OxFloodNet/sensor-device/OXFloodNet_Dispay/logo.h

// Settings are Orientation: Horizontal
// Byte order: LSB First
//const unsigned char OxFloodNet[] = {
static const unsigned char OxFloodNet[] PROGMEM = {
    '\x00','\x00','\x00','\x00','\x00','\x00','\x00','\x00', // 0x0008
    '\x00','\x00','\x00','\x00','\x00','\x00','\x00','\x00', // 0x0018
    '\x00','\x00','\x00','\x00','\x00','\x00','\x00','\x00', // 0x0028
    '\x00','\x00','\x00','\x00','\x00','\x00','\x00','\x00', // 0x0038
    '\x00','\x00','\x00','\x00','\x00','\x00','\x00','\x00', // 0x0048
    '\x00','\x00','\x00','\x00','\x00','\x00','\x00','\x00', // 0x0058
    '\x00','\x00','\x00','\x00','\x00','\x00','\x00','\x00', // 0x0068
    '\x00','\x00','\x00','\x00','\x00','\x00','\x00','\x00', // 0x0078
    '\x00','\x00','\x00','\x00','\x00','\x00','\x00','\x00', // 0x0088
    '\x00','\x00','\x00','\x00','\x00','\x00','\x00','\x00', // 0x0098
    '\x00','\x00','\x00','\x00','\x00','\x00','\x00','\x00', // 0x00a8
    '\x00','\x00','\x00','\x00','\x00','\x00','\x00','\x00', // 0x00b8
    '\x00','\x00','\x00','\x00','\x00','\x00','\x00','\x00', // 0x00c8
    '\x00','\x00','\x00','\x00','\x00','\x00','\x00','\x00', // 0x00d8
    '\x00','\x00','\x00','\x00','\x00','\x00','\x00','\x00', // 0x00e8
    '\x00','\x00','\x00','\x00','\x00','\x00','\x00','\x00', // 0x00f8
    '\x00','\x00','\x00','\x00','\x00','\x00','\x00','\x00', // 0x0108
    '\x00','\x00','\x00','\x00','\x00','\x00','\x00','\x00', // 0x0118
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
    '\x00','\x01','\xff','\xff','\xff','\xff','\xff','\xff', // 0x0848
    '\xff','\xf8','\x00','\x38','\x00','\x00','\x30','\x00', // 0x0858
    '\x00','\x01','\xff','\xff','\xff','\xff','\xff','\xff', // 0x0868
    '\xff','\xf8','\x00','\x78','\x00','\x00','\x38','\x00', // 0x0878
    '\x00','\x01','\xff','\xff','\xff','\xff','\xff','\xff', // 0x0888
    '\xff','\xf8','\x00','\xf0','\x00','\x00','\x38','\x00', // 0x0898
    '\x00','\x01','\xff','\xff','\xff','\xff','\xff','\xff', // 0x08a8
    '\xff','\xf8','\x03','\xff','\x00','\x00','\x38','\x00', // 0x08b8
    '\x00','\x01','\xff','\xff','\xff','\xff','\xff','\xff', // 0x08c8
    '\xff','\xf8','\x03','\xff','\xfe','\x00','\x18','\x00', // 0x08d8
    '\x00','\x01','\xff','\xff','\xff','\xff','\xff','\xff', // 0x08e8
    '\xff','\xf8','\x07','\xff','\xff','\xf8','\x1c','\x00', // 0x08f8
    '\x00','\x01','\xff','\xff','\xff','\xff','\xff','\xff', // 0x0908
    '\xff','\xf8','\x07','\x8f','\xff','\xff','\xfc','\x00', // 0x0918
    '\x00','\x01','\xff','\xff','\xff','\xff','\xff','\xff', // 0x0928
    '\xff','\xf8','\x07','\x07','\xff','\xff','\xfe','\x00', // 0x0938
    '\x00','\x01','\xff','\xff','\xff','\xff','\xff','\xff', // 0x0948
    '\xff','\xf8','\x07','\x07','\xff','\xff','\xff','\x00', // 0x0958
    '\x00','\x01','\xff','\xff','\xff','\xff','\xff','\xff', // 0x0968
    '\xff','\xf8','\x07','\x0f','\xff','\xff','\xdf','\x00', // 0x0978
    '\x00','\x01','\xff','\xff','\xff','\xff','\xff','\xff', // 0x0988
    '\xff','\xf8','\x0f','\xdf','\xff','\xff','\x87','\x80', // 0x0998
    '\x00','\x01','\x87','\xff','\xff','\xff','\xff','\xff', // 0x09a8
    '\xff','\xf8','\x0f','\xff','\xff','\xe1','\x07','\x80', // 0x09b8
    '\x00','\x00','\x00','\x7f','\xff','\xf0','\x03','\xff', // 0x09c8
    '\xff','\xc0','\x0f','\xff','\xfe','\x00','\x07','\x00', // 0x09d8
    '\x00','\x00','\x00','\x1f','\xff','\xc0','\x00','\xff', // 0x09e8
    '\xfe','\x00','\x03','\xff','\xf0','\x00','\x07','\x00', // 0x09f8
    '\x00','\x00','\x00','\x07','\xfe','\x00','\x00','\x1f', // 0x0a08
    '\xf8','\x00','\x00','\xff','\xc0','\x00','\x03','\x00', // 0x0a18
    '\x00','\x00','\x00','\x00','\x00','\x00','\x00','\x00', // 0x0a28
    '\x00','\x00','\x00','\x00','\x00','\x00','\x00','\x00', // 0x0a38
    '\x00','\x00','\x00','\x00','\x00','\x00','\x00','\x00', // 0x0a48
    '\x00','\x00','\x00','\x00','\x00','\x00','\x00','\x00', // 0x0a58
    '\x00','\x00','\x00','\x00','\x00','\x00','\x00','\x00', // 0x0a68
    '\x00','\x00','\x00','\x00','\x00','\x00','\x00','\x00', // 0x0a78
    '\x00','\x00','\x00','\x00','\x00','\x00','\x00','\x00', // 0x0a88
    '\x00','\x00','\x00','\x00','\x00','\x00','\x00','\x00', // 0x0a98
    '\x00','\x00','\x00','\x00','\x00','\x00','\x00','\x00', // 0x0aa8
    '\x00','\x00','\x00','\x00','\x00','\x00','\x00','\x00', // 0x0ab8
    '\x00','\x00','\x00','\x00','\x00','\x00','\x00','\x00', // 0x0ac8
    '\x00','\x00','\x00','\x00','\x00','\x00','\x00','\x00', // 0x0ad8
    '\x00','\x00','\xfe','\x00','\x00','\x03','\xe0','\x00', // 0x0ae8
    '\x00','\x0f','\x80','\x00','\x00','\x7f','\x00','\x00', // 0x0af8
    '\x00','\x07','\xff','\xc0','\x00','\x1f','\xfe','\x00', // 0x0b08
    '\x00','\x7f','\xf0','\x00','\x03','\xff','\xe0','\x00', // 0x0b18
    '\x00','\x1f','\xff','\xf0','\x00','\x7f','\xff','\x80', // 0x0b28
    '\x01','\xff','\xfc','\x00','\x0f','\xff','\xf0','\x00', // 0x0b38
    '\x01','\xff','\xff','\xfc','\x03','\xff','\xff','\xf0', // 0x0b48
    '\x1f','\xff','\xff','\x80','\x7f','\xff','\xff','\x00', // 0x0b58
    '\x07','\xff','\xff','\xff','\xff','\xff','\xff','\xff', // 0x0b68
    '\xff','\xff','\xff','\xff','\xff','\xff','\xff','\xe0', // 0x0b78
    '\x07','\xff','\xff','\xff','\xff','\xff','\xff','\xff', // 0x0b88
    '\xff','\xff','\xff','\xff','\xff','\xff','\xff','\xe0', // 0x0b98
    '\x07','\xff','\xff','\xff','\xff','\xff','\xff','\xff', // 0x0ba8
    '\xff','\xff','\xff','\xff','\xff','\xff','\xff','\xe0', // 0x0bb8
    '\x07','\xff','\xff','\xff','\xff','\xff','\xff','\xff', // 0x0bc8
    '\xff','\xff','\xff','\xff','\xff','\xff','\xff','\xe0', // 0x0bd8
    '\x07','\xff','\xff','\xff','\xff','\xff','\xff','\xff', // 0x0be8
    '\xff','\xff','\xff','\xff','\xff','\xff','\xff','\xe0', // 0x0bf8
    '\x07','\xff','\xff','\xff','\xff','\xff','\xff','\xff', // 0x0c08
    '\xff','\xff','\xff','\xff','\xff','\xff','\xff','\xe0', // 0x0c18
    '\x07','\xff','\xff','\xff','\xff','\xff','\xff','\xff', // 0x0c28
    '\xff','\xff','\xff','\xff','\xff','\xff','\xff','\xe0', // 0x0c38
    '\x07','\xff','\xff','\xff','\xff','\xff','\xff','\xff', // 0x0c48
    '\xff','\xff','\xff','\xff','\xff','\xff','\xff','\xe0', // 0x0c58
    '\x07','\xff','\xff','\xff','\xff','\xff','\xff','\xff', // 0x0c68
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
    '\x00','\x00','\x00','\x00','\x00','\x00','\x00','\x00', // 0x0f48
    '\x00','\x00','\x00','\x00','\x00','\x00','\x00','\x00', // 0x0f58
    '\x00','\x00','\x00','\x00','\x00','\x00','\x00','\x00', // 0x0f68
    '\x00','\x00','\x00','\x00','\x00','\x00','\x00','\x00', // 0x0f78
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
};
