OxFloodNet/sensor-device/OXFloodNet_Dispay/heart.h

//const unsigned char heart[] =
static const unsigned char heart[] PROGMEM = {
    '\x01','\xc0','\x03','\x80','\x0f','\xf8','\x1f','\xf0', // 0x0008
    '\x1f','\xfc','\x3f','\xf8','\x3f','\xfe','\x7f','\xfc', // 0x0018
    '\x3f','\xff','\xff','\xfc','\x7f','\xff','\xff','\xfe', // 0x0028
    '\x7f','\xff','\xff','\xfe','\x7f','\xff','\xff','\xff', // 0x0038
    '\xff','\xff','\xff','\xff','\xff','\xff','\xff','\xff', // 0x0048
    '\xff','\xff','\xff','\xff','\xff','\xff','\xff','\xff', // 0x0058
    '\xff','\xff','\xff','\xff','\xff','\xff','\xff','\xff', // 0x0068
    '\x7f','\xff','\xff','\xff','\x7f','\xff','\xff','\xfe', // 0x0078
    '\x7f','\xff','\xff','\xfe','\x3f','\xff','\xff','\xfe', // 0x0088
    '\x3f','\xff','\xff','\xfc','\x3f','\xff','\xff','\xfc', // 0x0098
    '\x1f','\xff','\xff','\xf8','\x0f','\xff','\xff','\xf0', // 0x00a8
    '\x0f','\xff','\xff','\xf0','\x07','\xff','\xff','\xe0', // 0x00b8
    '\x03','\xff','\xff','\xc0','\x01','\xff','\xff','\x80', // 0x00c8
    '\x00','\xff','\xff','\x00','\x00','\x7f','\xfe','\x00', // 0x00d8
    '\x00','\x3f','\xfc','\x00','\x00','\x1f','\xf8','\x00', // 0x00e8
    '\x00','\x07','\xe0','\x00','\x00','\x03','\xc0','\x00', // 0x00f8
};
